patryksitarek/domowaStacjaMeteo/Images/chartExample.jpg

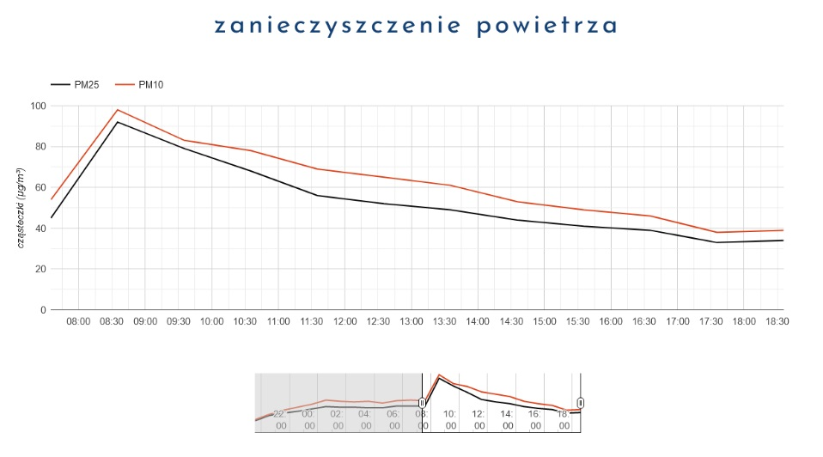
Images/chartExample.jpg
