patryksitarek/domowaStacjaMeteo/Images/rainGauge1.jpg

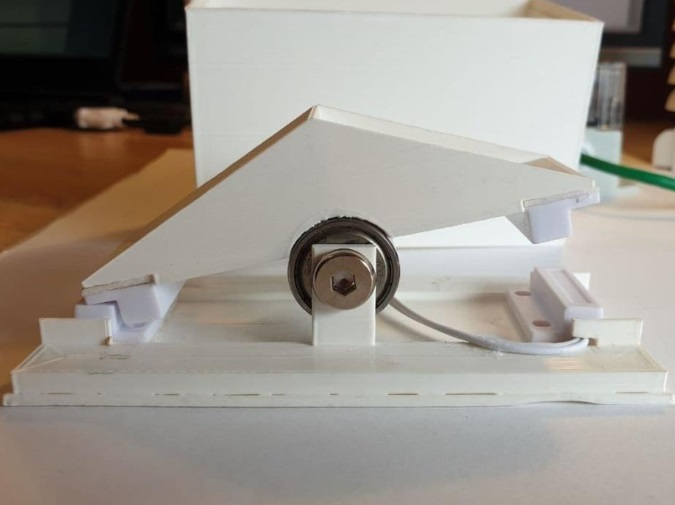
Images/rainGauge1.jpg
